p123ad/e_paper_picture_frame/code/main/Pictures.h

#include "Image1Data.h"
#include "Image2Data.h"
#include "Image3Data.h"
#include "Image4Data.h"
#include "Image5Data.h"
#include "Image6Data.h"
#include "Image7Data.h"
#include "Image8Data.h"
#include "Image9Data.h"
#include "Image10Data.h"
#include "Image11Data.h"
#include "Image12Data.h"
#include "Image13Data.h"
#include "Image14Data.h"
#include "Image15Data.h"
#include "Image16Data.h"
#include "Image17Data.h"
